dallinlmag/RocketLeagueBall/Rocket_League_ball_with_LEDs_and_stand/images/248eec35b3bdb365904e13abe7d99484_preview_featured.jpg

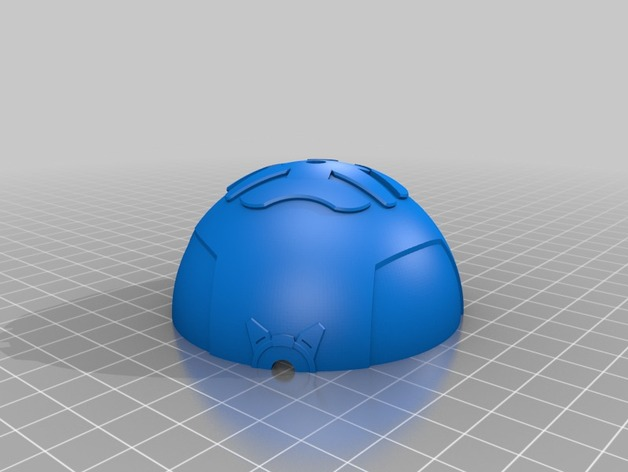
Rocket_League_ball_with_LEDs_and_stand/images/248eec35b3bdb365904e13abe7d99484_preview_featured.jpg
