dallinlmag/RocketLeagueBall/Rocket_League_ball_with_LEDs_and_stand/images/534da0bb036d7f063b027a49b1cd8d4f_preview_featured.jpg

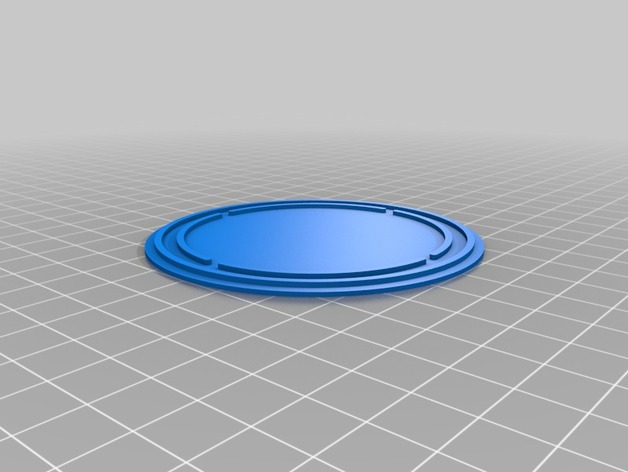
Rocket_League_ball_with_LEDs_and_stand/images/534da0bb036d7f063b027a49b1cd8d4f_preview_featured.jpg
